namor5772/WifiRadio3/Images/ABC_Double_j.png

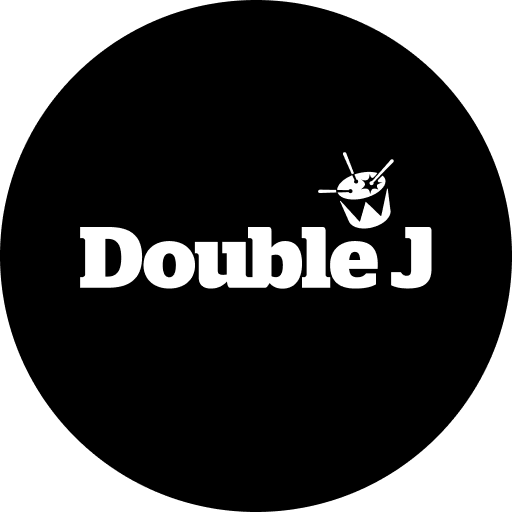
Images/ABC_Double_j.png
