namor5772/WifiRadio3/Images/ABC_Radio_National.png

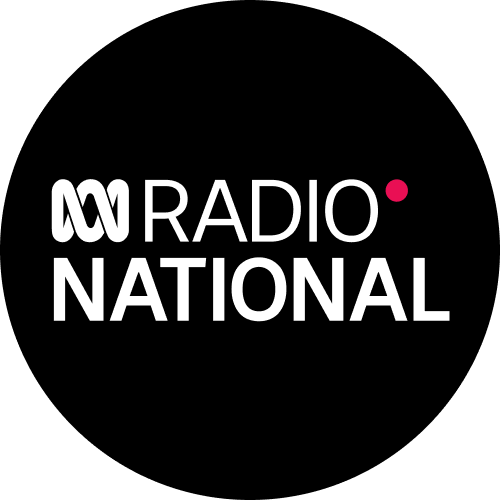
Images/ABC_Radio_National.png
