namor5772/WifiRadio3/Images/ABC_Radio_National_LIVE.jpg

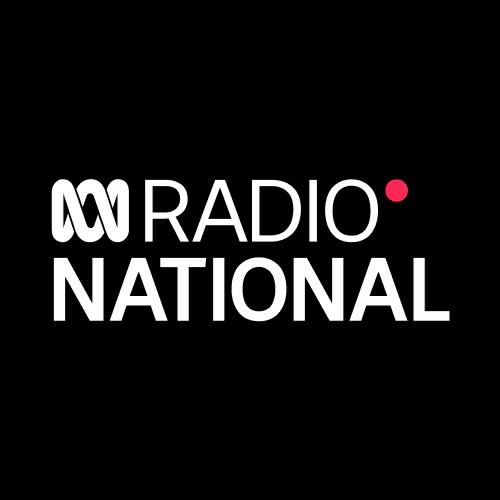
Images/ABC_Radio_National_LIVE.jpg
