namor5772/WifiRadio3/Images/ABC_triple_j.jpg

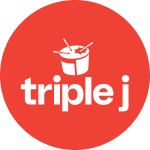
Images/ABC_triple_j.jpg
