namor5772/WifiRadio3/Images/ABC_triple_j_Hottest.png

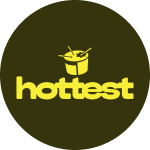
Images/ABC_triple_j_Hottest.png
