namor5772/WifiRadio3/Images/ABC_triple_j_Unearthed.png

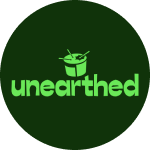
Images/ABC_triple_j_Unearthed.png
