namor5772/WifiRadio3/Images/Cable copy.png

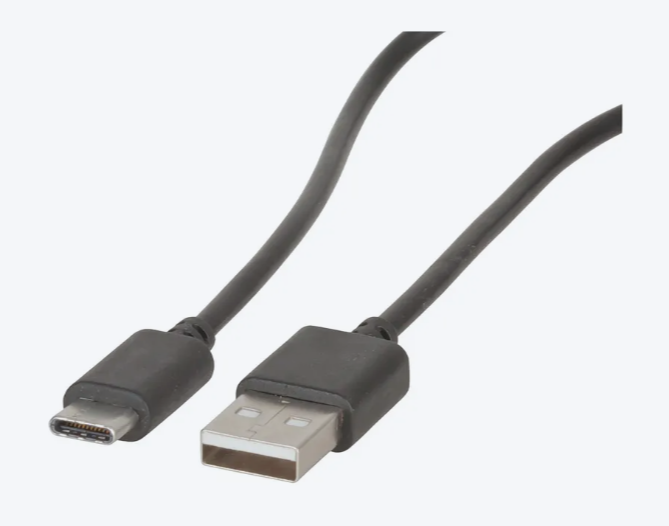
Images/Cable copy.png
