namor5772/WifiRadio3/Images/Card copy.png

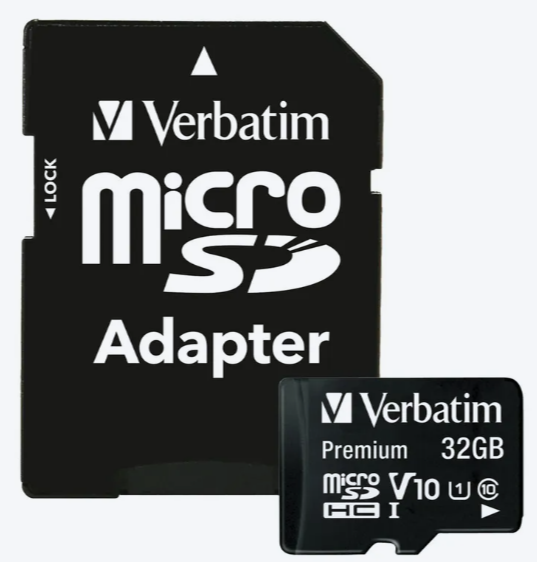
Images/Card copy.png
