namor5772/WifiRadio3/Images/Header2 copy.png

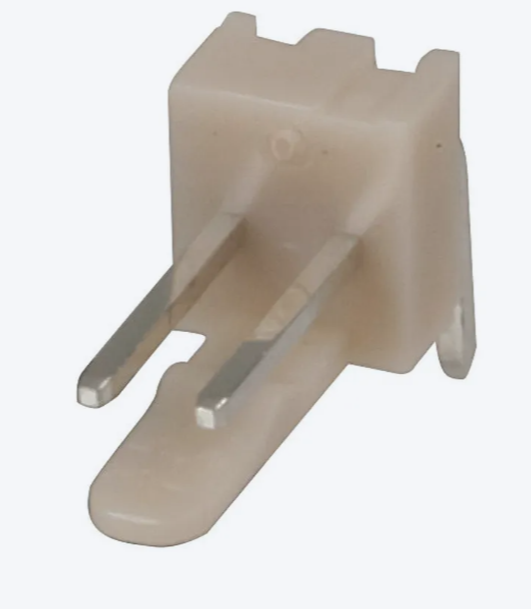
Images/Header2 copy.png
