namor5772/WifiRadio3/Images/LED.png

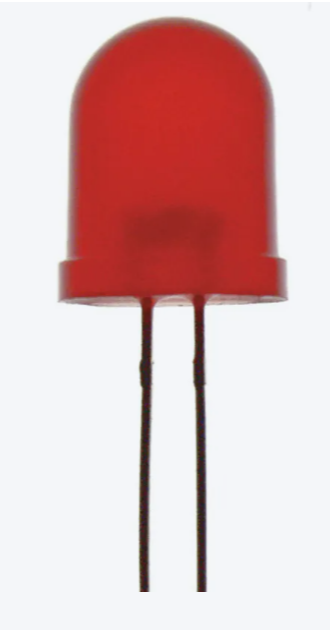
Images/LED.png
