namor5772/WifiRadio3/Images/presenter.jpg

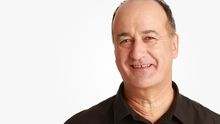
Images/presenter.jpg
