namor5772/WifiRadio3/Images/RPI4B.png

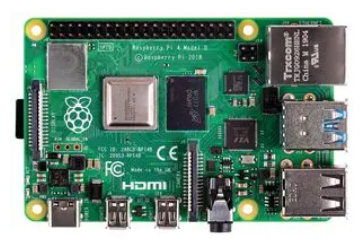
Images/RPI4B.png
