namor5772/WifiRadio3/Images/Switch.png

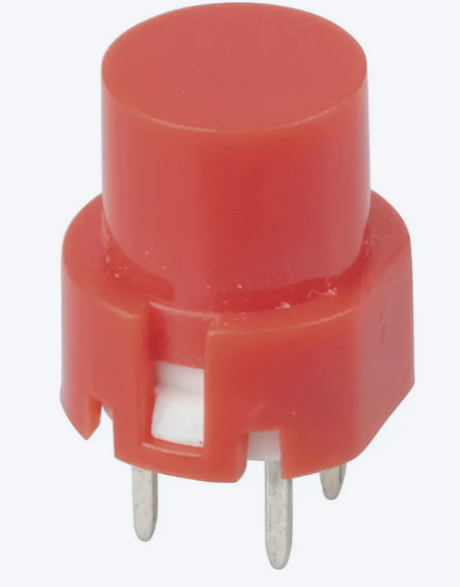
Images/Switch.png
