namor5772/WifiRadio3/Images/Wire.png

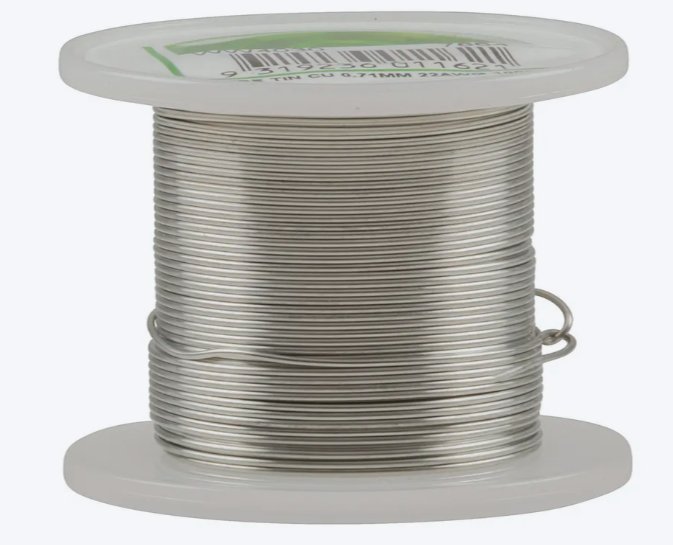
Images/Wire.png
